ahmadq122/Digital-Weighing-Scale-Board-6-Channels/src/RTOS/RTOS.cpp

#if CONFIG_FREERTOS_UNICORE
#define ARDUINO_RUNNING_CORE 0
#else
#define ARDUINO_RUNNING_CORE 1
#endif

#include "RTOS.h"
#include "Nextion/Nextion.h"
#include "FlashMemory/FlashMemory.h"
#include "ADC/ADS1232.h"
#include "Datalogger/Datalogger.h"

//Define the tasks
void Task_01(void *pvParameters);
void Task_02(void *pvParameters);
void Task_03(void *pvParameters); //millis()
void Task_04(void *pvParameters); //ADS Board 1
void Task_05(void *pvParameters); //ADS Board 2
void Task_06(void *pvParameters); //ADS Board 3
void Task_07(void *pvParameters); //Remote log
// void Task_08(void *pvParameters); //Battery Monitoring

// the setup function runs once when you press reset or power the board
void RealTimeOS::setup(void)
{
    // Now set up two tasks to run independently.
    xTaskCreatePinnedToCore(
        Task_01,
        "Task_01", // A name just for humans
        1024 * 2,  // This stack size can be checked & adjusted by reading the Stack Highwater
        NULL,
        configMAX_PRIORITIES - 1, // Priority, with 3 (configMAX_PRIORITIES - 1) being the highest, and 0 being the lowest.
        NULL,
        ARDUINO_RUNNING_CORE);

    xTaskCreatePinnedToCore(
        Task_02,
        "Task_02",
        1024 * 2, // Stack size
        NULL,
        configMAX_PRIORITIES - 2, // Priority
        NULL,
        ARDUINO_RUNNING_CORE);

    xTaskCreatePinnedToCore(
        Task_03,
        "Task_03",
        1024, // Stack size
        NULL,
        configMAX_PRIORITIES - 3, // Priority
        NULL,
        ARDUINO_RUNNING_CORE);

    xTaskCreatePinnedToCore(
        Task_04,
        "Task_04",
        1024 * 5, // Stack size
        NULL,
        configMAX_PRIORITIES - 4, // Priority
        NULL,
        ARDUINO_RUNNING_CORE);

    xTaskCreatePinnedToCore(
        Task_05,
        "Task_05",
        1024 * 5, // Stack size
        NULL,
        configMAX_PRIORITIES - 5, // Priority
        NULL,
        ARDUINO_RUNNING_CORE);

    xTaskCreatePinnedToCore(
        Task_06,
        "Task_06",
        1024 * 5, // Stack size
        NULL,
        configMAX_PRIORITIES - 6, // Priority
        NULL,
        ARDUINO_RUNNING_CORE);

    xTaskCreatePinnedToCore(
        Task_07,
        "Task_07",
        1024 * 10, // Stack size
        NULL,
        configMAX_PRIORITIES - 7, // Priority
        NULL,
        ARDUINO_RUNNING_CORE);

    // xTaskCreatePinnedToCore(
    //     Task_08,
    //     "Task_08",
    //     1024 * 2, // Stack size
    //     NULL,
    //     configMAX_PRIORITIES - 8, // Priority
    //     NULL,
    //     ARDUINO_RUNNING_CORE);
}

/*--------------------------------------------------*/
/*---------------------- Tasks ---------------------*/
/*--------------------------------------------------*/

void Task_01(void *pvParameters) // This is a task.
{
    (void)pvParameters;

    for (;;) // A Task shall never return or exit.
    {
        if (++rtos.counterUpSeconds == 0xFFFFFFFFFF)
            rtos.counterUpSeconds = 0;

        if (rtos.counterDownSeconds)
            rtos.counterDownSeconds--;
        if (rtos.counterDownSecondsBattLow)
            rtos.counterDownSecondsBattLow--;

        if (rtos.counterDownSecondsLog[serial])
            rtos.counterDownSecondsLog[serial]--;
        if (rtos.counterDownSecondsLog[local])
            rtos.counterDownSecondsLog[local]--;
        if (rtos.counterDownSecondsLog[remote])
            rtos.counterDownSecondsLog[remote]--;

        if (++rtos.interruptSeconds > 59)
        {
            rtos.minuteTriggered = true;
            rtos.interruptSeconds = 0;
        }

        if (rtos.interruptSeconds % 5 == 0 && !rtos.wifiConnectionTriggered)
            rtos.wifiConnectionTriggered = true;

        for (uint8_t i = 0; i < 10; i++)
        {
            rtos.secondTriggered[i] = 1;
        }

        if (data.getDimScreenTimer() > 0)
        {
            if (rtos.dimmCounterDownSecond)
                rtos.dimmCounterDownSecond--;
            else
            {
                if (rtos.currentBrightness > Auto_Dim_Brightness)
                {
                    rtos.currentBrightness = Auto_Dim_Brightness;
                    hmi.setIntegerToNextion("dim", rtos.currentBrightness);
                }
            }
        }

        rtos.secondBlink = !rtos.secondBlink;
        vTaskDelay(1000); // Delay for 1 second
    }
}

void Task_02(void *pvParameters) // This is a task.
{
    (void)pvParameters;

    for (;;) // A Task shall never return or exit.
    {
        hmi.serialEvent_2();
        vTaskDelay(30); // Delay for 1 second
    }
}

void Task_03(void *pvParameters) // This is a task.
{
    (void)pvParameters;

    for (;;) // A Task shall never return or exit.
    {
        if (++rtos.milliSeconds >= 0xFFFFFFFFFFFFFFFF)
            rtos.milliSeconds = 0;
        vTaskDelay(1); // Delay for 1 milli second
        // if (rtos.milliSeconds % 100 == 0)
        //     Serial.println(rtos.milliSeconds);
    }
}

void Task_04(void *pvParameters) // This is a task.
{
    (void)pvParameters;

    bool channel = false;
    uint8_t counter = 0;
    uint8_t board = ads1;

    if (ads.init(board))
    {
        ads.isAvailable[board] = true;
        for (;;) // A Task shall never return or exit.
        {
            if (data.getChannelEnDisStatus(channel))
            {
                if (ads.dataRead(board, channel, 1))
                {
                    if (++counter > 1)
                    {
                        counter = 0;
                        if (data.getChannelEnDisStatus(!channel))
                            channel = !channel;
                    }
                }
                vTaskDelay(20);
            }
            else
            {
                if (data.getChannelEnDisStatus(!channel))
                    channel = !channel;
                vTaskDelay(1000);
            }
        }
    }
    else
    {
        for (;;)
        {
            // Serial.println("Do Nothing1!");
            vTaskDelay(10000);
            //do noting
        }
    }
}

void Task_05(void *pvParameters) // This is a task.
{
    (void)pvParameters;

    bool channel = false;
    uint8_t counter = 0;
    uint8_t board = ads2;

    if (ads.init(board))
    {
        ads.isAvailable[board] = true;
        for (;;) // A Task shall never return or exit.
        {
            if (data.getChannelEnDisStatus(2 + channel))
            {
                if (ads.dataRead(board, channel, 1))
                {
                    if (++counter > 2)
                    {
                        counter = 0;
                        if (data.getChannelEnDisStatus(2 + !channel))
                            channel = !channel;
                    }
                }
                vTaskDelay(20);
            }
            else
            {
                if (data.getChannelEnDisStatus(!channel))
                    channel = !channel;
                vTaskDelay(1000);
            }
        }
    }
    else
    {
        for (;;)
        {
            // Serial.println("Do Nothing2!");
            vTaskDelay(10000);
            //do noting
        }
    }
}
void Task_06(void *pvParameters) // This is a task.
{
    (void)pvParameters;

    bool channel = false;
    uint8_t counter = 0;
    uint8_t board = ads3;

    if (ads.init(board))
    {
        ads.isAvailable[board] = true;
        for (;;) // A Task shall never return or exit.
        {
            if (data.getChannelEnDisStatus(4 + channel))
            {
                if (ads.dataRead(board, channel, 1))
                {
                    if (++counter > 1)
                    {
                        counter = 0;
                        if (data.getChannelEnDisStatus(4 + !channel))
                            channel = !channel;
                    }
                }
                vTaskDelay(20);
            }
            else
            {
                if (data.getChannelEnDisStatus(!channel))
                    channel = !channel;
                vTaskDelay(1000);
            }
        }
    }
    else
    {
        for (;;)
        {
            // Serial.println("Do Nothing3!");
            vTaskDelay(10000);
            //do noting
        }
    }
}

void Task_07(void *pvParameters) // This is a task.
{
    (void)pvParameters;

    for (;;) // A Task shall never return or exit.
    {
        for (uint8_t i = 0; i < 6; i++)
        {
            if (rtos.remoteLogTriggered[i])
            {
                logger.remoteLogging(i);
                rtos.remoteLogTriggered[i] = false;
            }
        }
        vTaskDelay(1000); // Delay for 1 second
    }
}

// void Task_08(void *pvParameters) // This is a task.
// {
//     (void)pvParameters;

//     for (;;) // A Task shall never return or exit.
//     {
//         if()
//         vTaskDelay(1000); // Delay for 1 second
//     }
// }

void RealTimeOS::updateStartProgressBar(uint8_t add)
{
    startProgressBar += add;
    startProgressBar = constrain(startProgressBar, 0, 100);
    hmi.setIntegerToNextion("init.val", startProgressBar);
}



RealTimeOS rtos;
