ahmadq122/Digital-Weighing-Scale-Board-6-Channels/src/PictureListID.h

#pragma once

enum ListID
{
    Background,
    Start_Background,
    Start_Progress_Bkg,
    Start_Progress_Val,
    Home_Bkg_Normal_Btn,
    Home_Bkg_Prs_Btn,
    Home_Max_Bkg,
    Battery_Charging,
    Wifi_Signal_Progress_Bkg,
    Wifi_Signal_Progress_Val,
    Battery_Progress_Bkg,
    Battery_Progress_Val,
    Battery_Low,
    Network_List_Bkg,
    Network_List_Prs,
    Network_List_Select,
    Network_Config_Normal_Btn,
    Network_Config_Prs_Btn,
    Network_Scan_Progress_Bkg,
    Network_Scan_Progress_Val,
    Network_No_Found_Normal_Btn,
    Network_No_Found_Prs_Btn,
    Measurement_List_Bkg,
    Measurement_List_Prs,
    Measurement_List_Select,
    Keyboard_Layout_1_Bkg,
    Keyboard_Layout_2_Bkg,
    Keyboard_Layout_1_Prs,
    Keyboard_Layout_2_Prs,
    Numpad_Layout_Bkg,
    Numpad_Layout_Prs,
    Settings_Menu_Normal_Btn,
    Settings_Menu_Prs_Btn,
    Settings1_Menu_Normal_Btn,
    Settings1_Menu_Prs_Btn,
    Settings11_Menu_Normal_Btn,
    Settings11_Menu_Prs_Btn,
    Settings1_Menu_Popup,
    Settings1_Menu_Popup_Prs,
    Timezone_Menu_Normal_Btn,
    Timezone_Menu_Prs_Btn,
    Timezone_Menu_Selected_Bkg,
    Brightness_Normal_Bkg,
    Brightness_Prs_PopBtn_Bkg,
    Brightness_Pogress_Cursor,
    Brightness_Prs_PopBtnBkg_Bkg,
    Maximum_List_Normal_Btn,
    Maximum_List_Prs_Btn,
    Time_Date_Normal_Bkg,
    Time_Date_Prs_Bkg,
    Debug_Normal_Btn,
    Debug_Prs_Btn,
    Debug_Baud_Select,
    Calibration_Menu_Normal_Btn,
    Calibration_Menu_Prs_Btn,
    Setpoint_Normal_Btn,
    Setpoint_Prs_Btn,
    Saving_Progress_Bkg,
    Saving_Progress_Val,
    Pointcal_Normal_Bkg,
    Pointcal_Prs_Bkg,
    Pointcal_Set_Bkg,
    Pointcal_Set_Prs_Bkg,
    Reset_Calib_Normal_Bkg,
    Reset_Calib_Prs_Bkg,
    Reset_Calib_Popup_Bkg,
    Reset_Calib_Popup_Prs_Bkg,
    Datalog_Menu_Normal_Btn,
    Datalog_Menu_Prs_Btn,
    Datalog_Serial_Normal_Bkg,
    Datalog_Serial_Prs_Bkg,
    Datalog_Local_Normal_Bkg,
    Datalog_Local_Prs_Bkg,
    Datalog_Remote_Normal_Bkg,
    Datalog_Remote_Prs_Bkg,
    Scheduler_Menu_Normal_Btn,
    Scheduler_Menu_Prs_Btn,
    Scheduler_Menu_Selected_Normal_Btn,
    Scheduler_Menu_Selected_Prs_Btn,
    Time_Scheduler_Normal_Bkg,
    Time_Scheduler_Prs_Bkg,
    Date_Scheduler_Normal_Bkg,
    Date_Scheduler_Prs_Bkg,

};
